isaac-art/Braidboard/3D/0119b/braidboardsmd v13.png

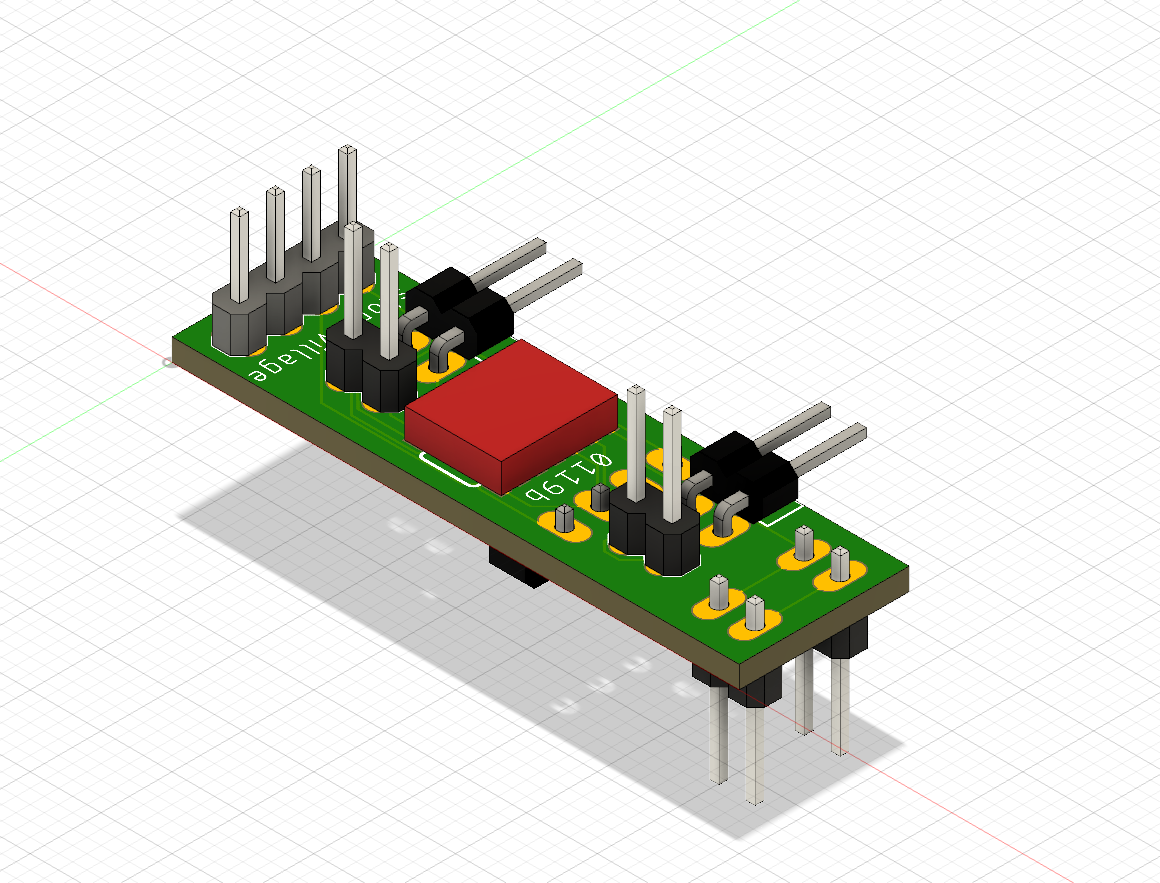
3D/0119b/braidboardsmd v13.png
