isaac-art/Braidboard/3D/0119b/mockup.png

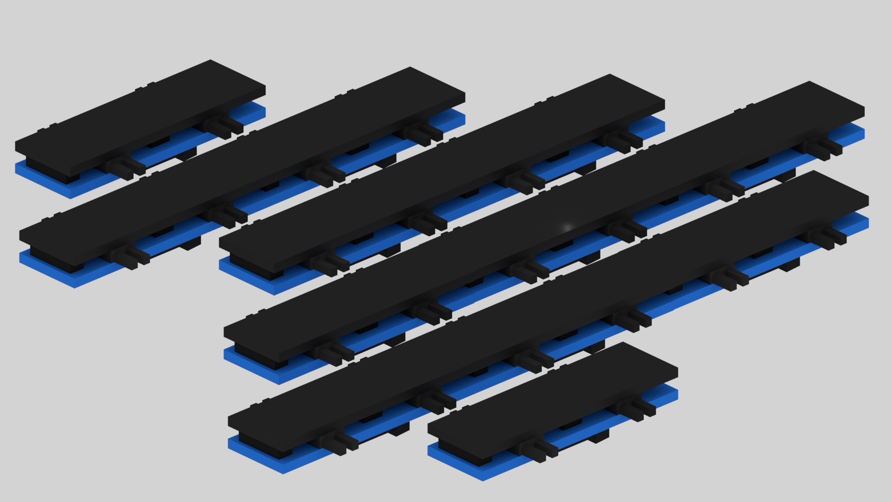
3D/0119b/mockup.png
