isaac-art/Braidboard/BOARD/0119b/braidboard_back.png

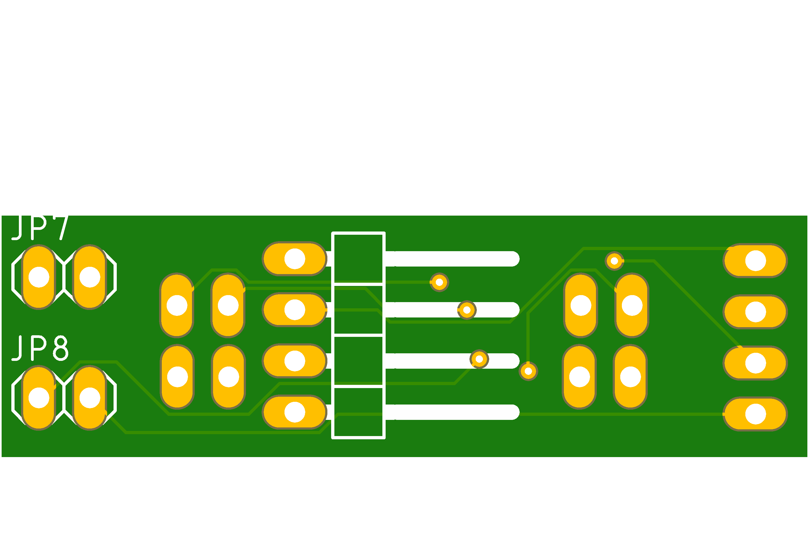
BOARD/0119b/braidboard_back.png
