isaac-art/Braidboard/BOARD/0119b/braidboard_front.png

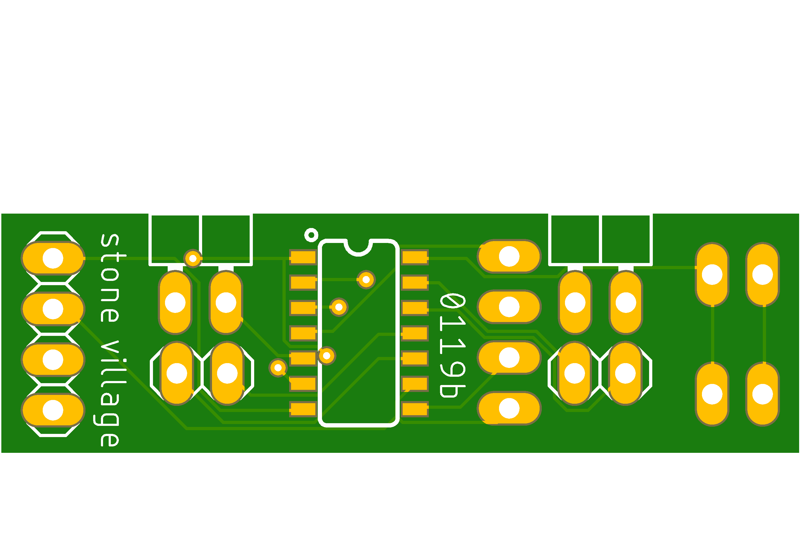
BOARD/0119b/braidboard_front.png
