isaac-art/Braidboard/PHOTOS/020119_250119/0119a.jpg

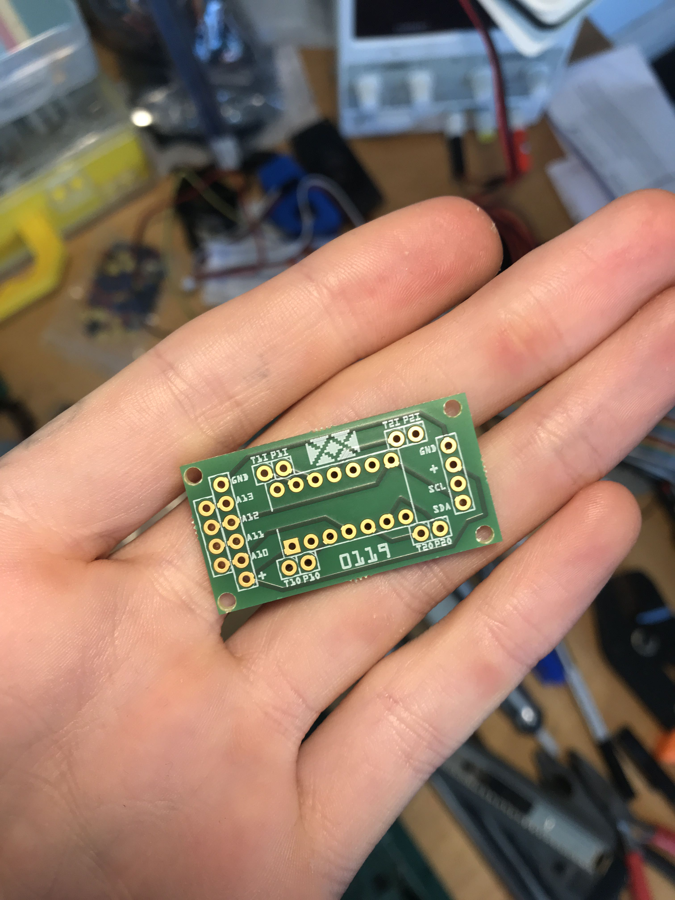
PHOTOS/020119_250119/0119a.jpg
