isaac-art/Braidboard/PHOTOS/020119_250119/IMG_2867.jpeg

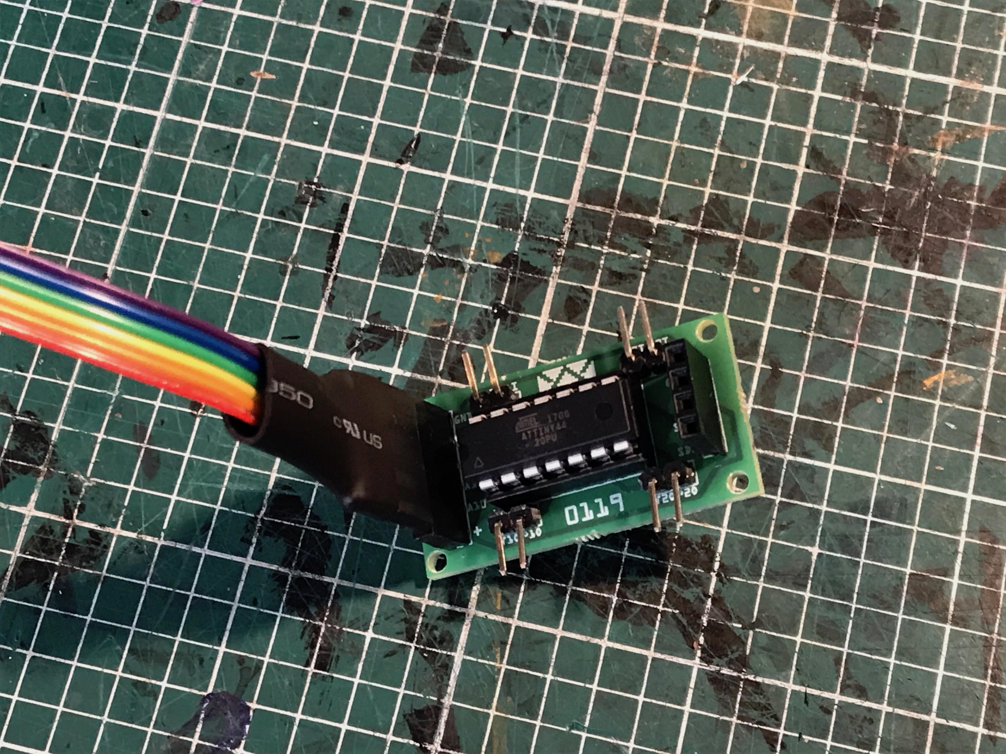
PHOTOS/020119_250119/IMG_2867.jpeg
