isaac-art/Braidboard/PHOTOS/020119_250119/IMG_2872.jpeg

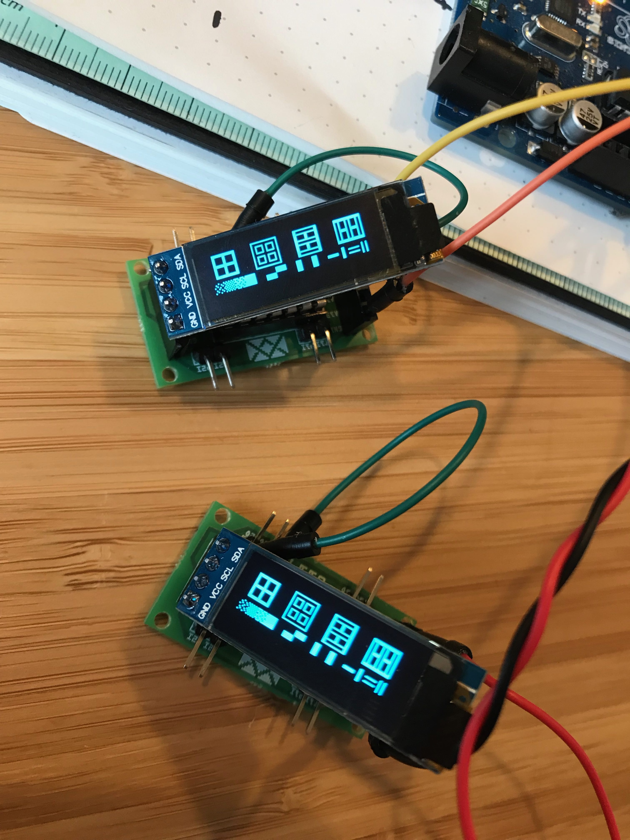
PHOTOS/020119_250119/IMG_2872.jpeg
