isaac-art/Braidboard/PHOTOS/020119_250119/IMG_2880.jpeg

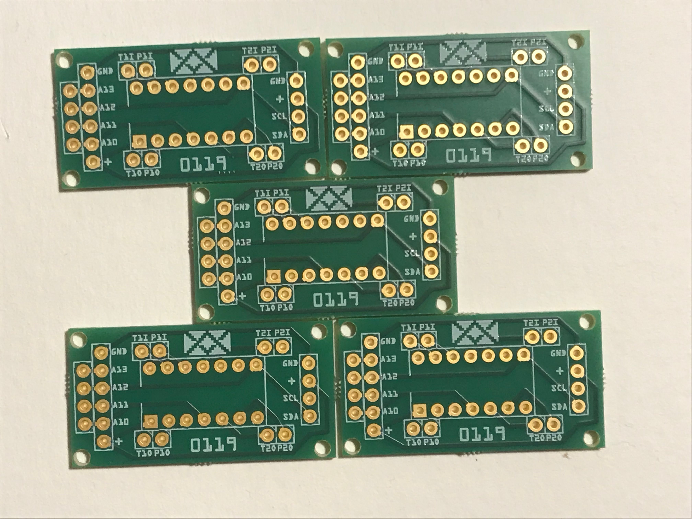
PHOTOS/020119_250119/IMG_2880.jpeg
