isaac-art/Braidboard/PHOTOS/020119_250119/IMG_2887.jpeg

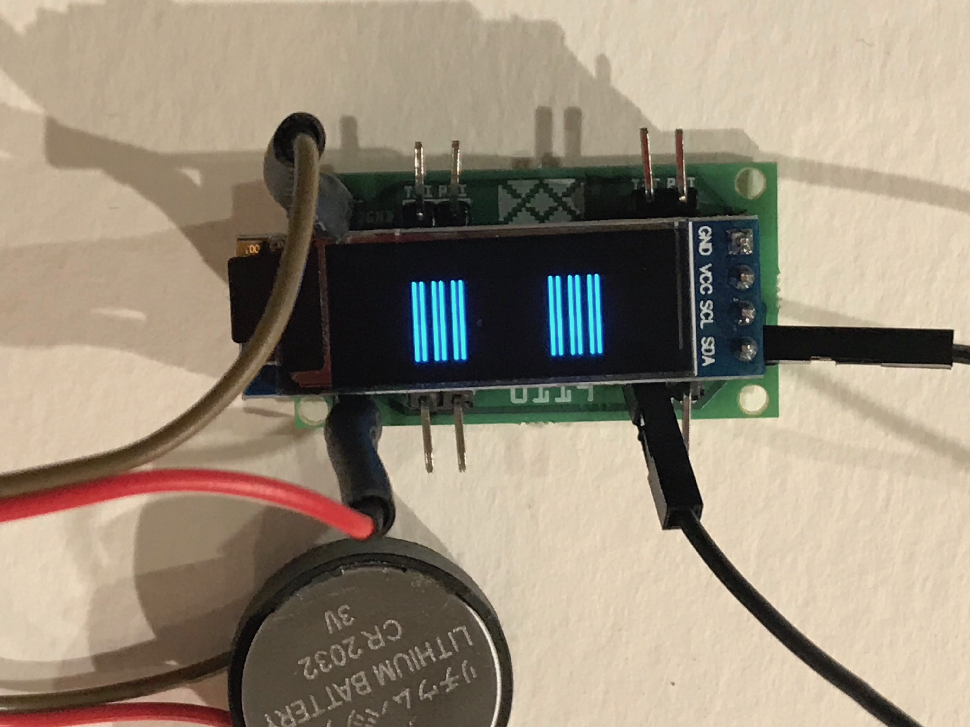
PHOTOS/020119_250119/IMG_2887.jpeg
