isaac-art/Braidboard/PHOTOS/260119_290119/IMG_2928.jpeg

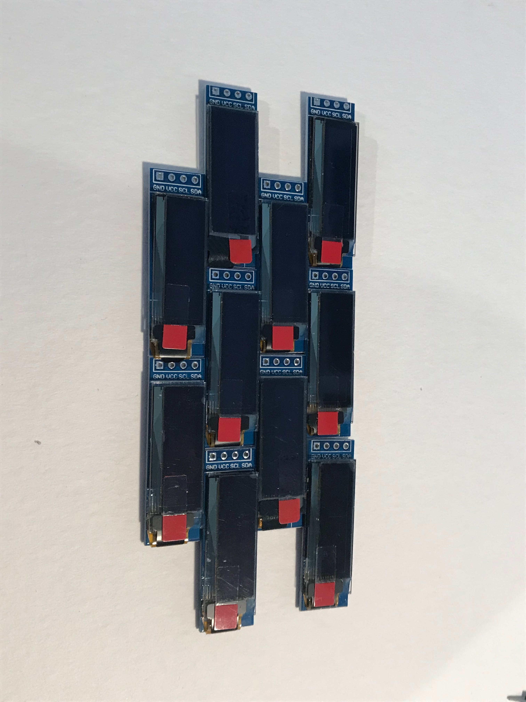
PHOTOS/260119_290119/IMG_2928.jpeg
