isaac-art/Braidboard/PHOTOS/260119_290119/IMG_2929.jpeg

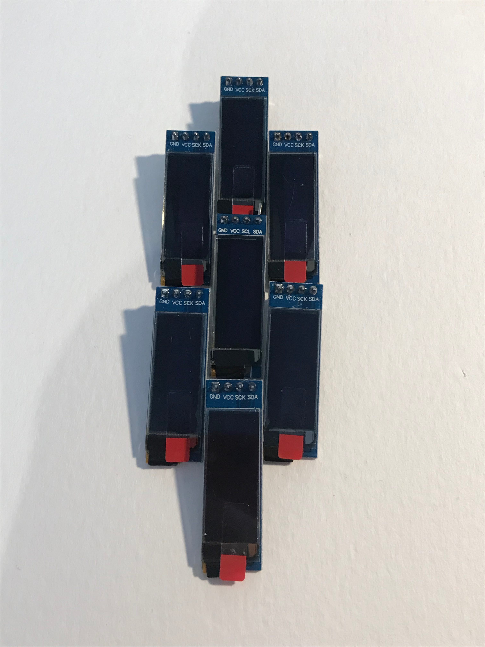
PHOTOS/260119_290119/IMG_2929.jpeg
