isaac-art/Braidboard/PHOTOS/260119_290119/IMG_2944.jpg

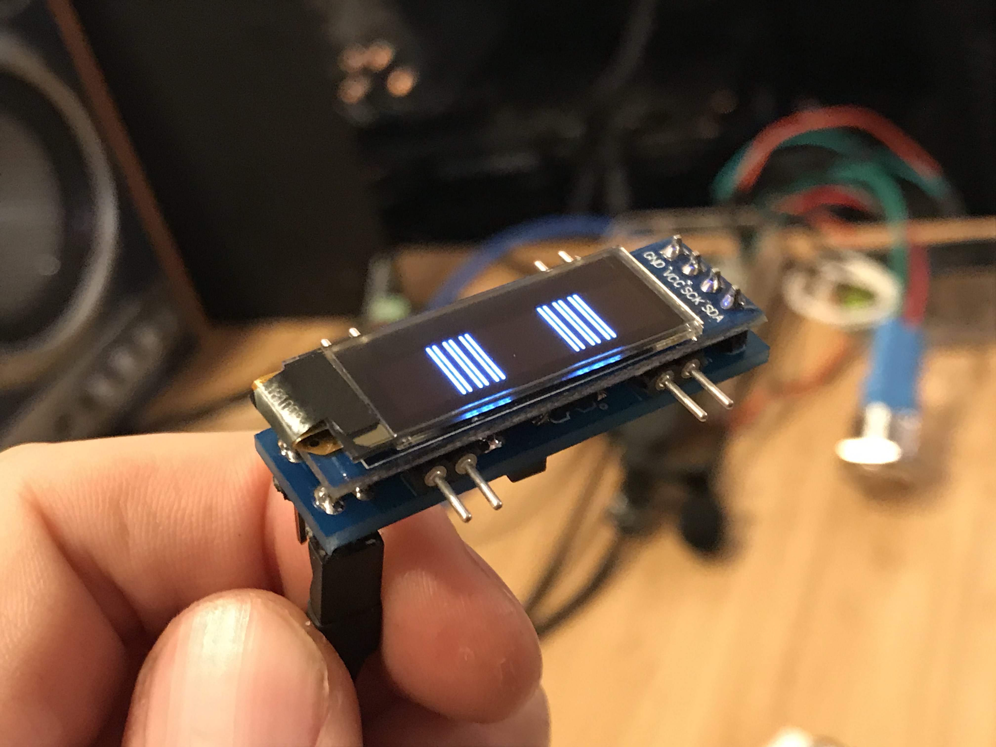
PHOTOS/260119_290119/IMG_2944.jpg
