isaac-art/Braidboard/PHOTOS/300119_010219/IMG_2962.jpeg

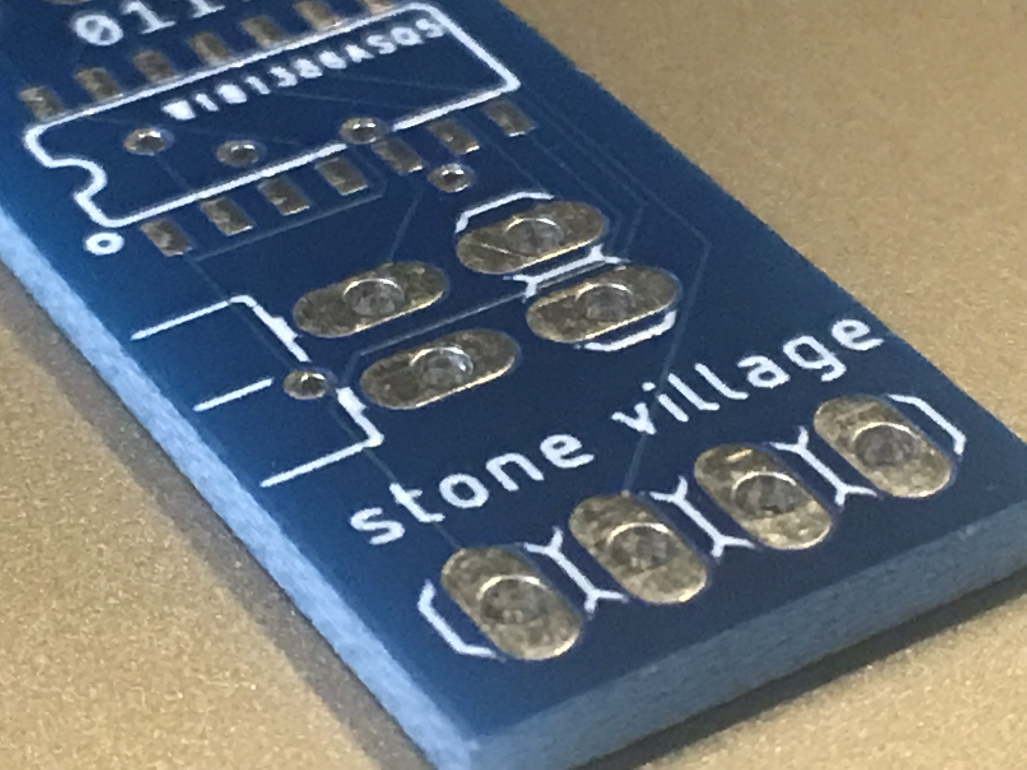
PHOTOS/300119_010219/IMG_2962.jpeg
