isaac-art/Braidboard/PHOTOS/300119_010219/IMG_2984.jpeg

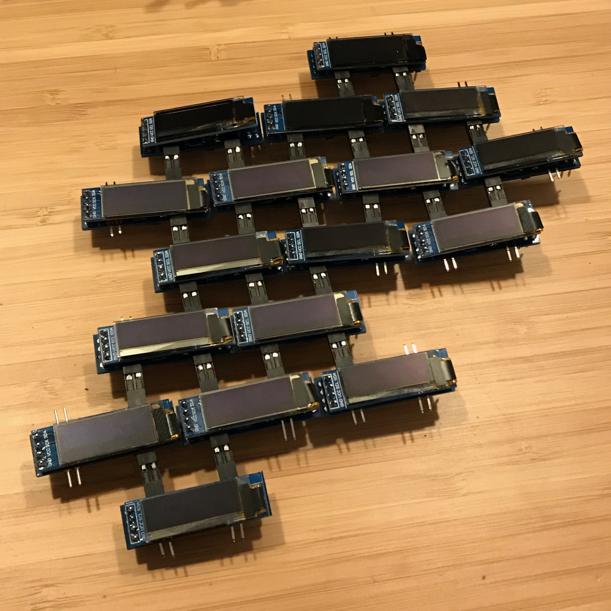
PHOTOS/300119_010219/IMG_2984.jpeg
