isaac-art/Braidboard/PHOTOS/300119_010219/IMG_3001.jpg

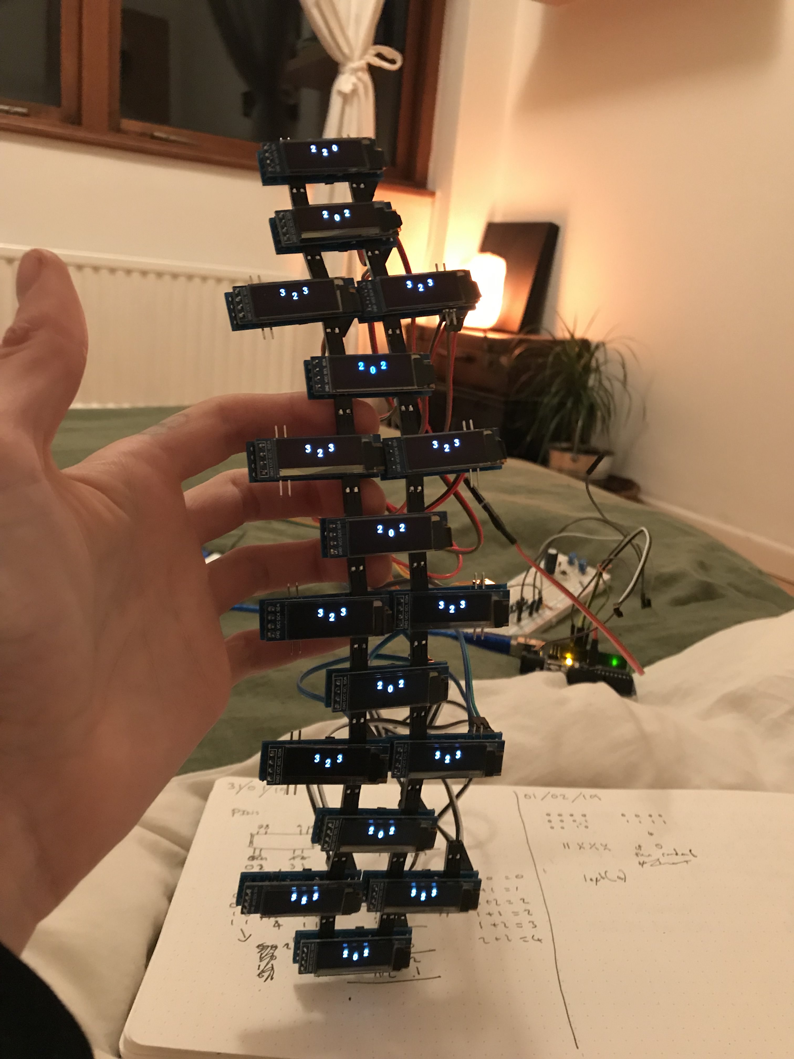
PHOTOS/300119_010219/IMG_3001.jpg
