isaac-art/Braidboard/PHOTOS/300119_010219/IMG_3003.jpeg

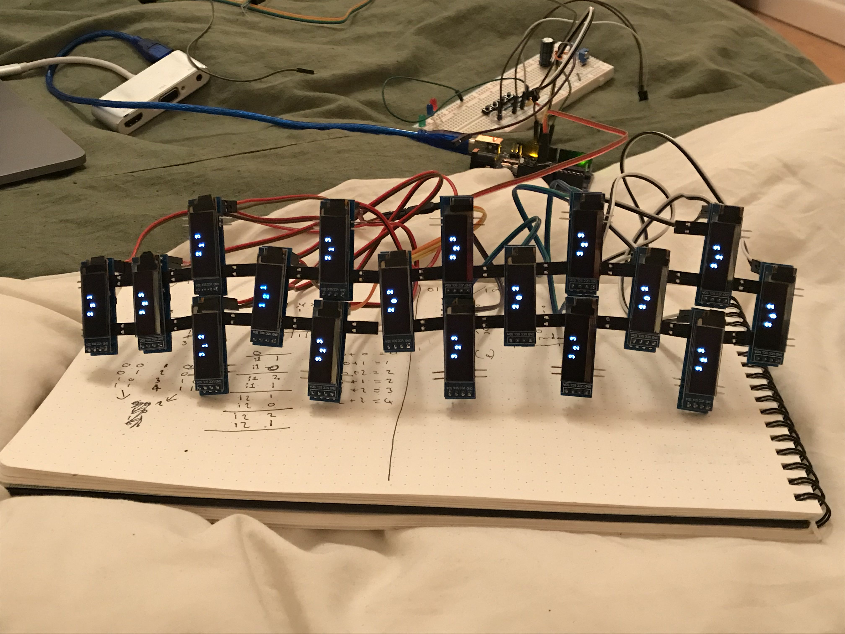
PHOTOS/300119_010219/IMG_3003.jpeg
