isaac-art/Braidboard/RESEARCH/2xmcp20317-i2c.jpg

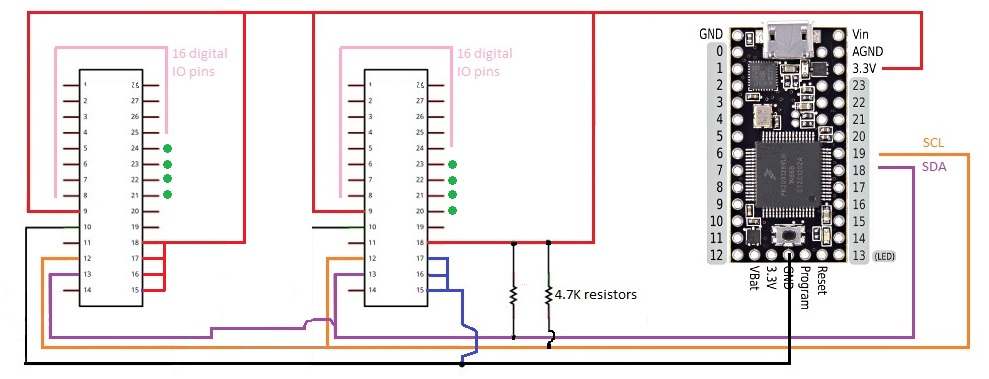
RESEARCH/2xmcp20317-i2c.jpg
