isaac-art/Braidboard/RESEARCH/52713d5b757b7fc0658b4567.png

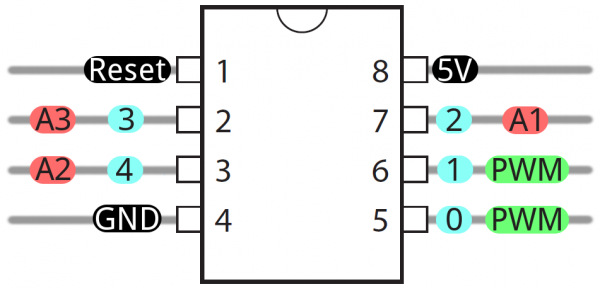
RESEARCH/52713d5b757b7fc0658b4567.png
