isaac-art/Braidboard/RESEARCH/Circuit-using-A3144-Hall-effect-Sensor.png

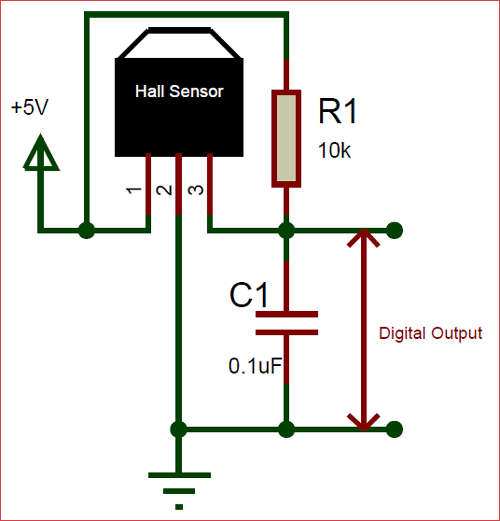
RESEARCH/Circuit-using-A3144-Hall-effect-Sensor.png
