isaac-art/Braidboard/RESEARCH/download-1.png

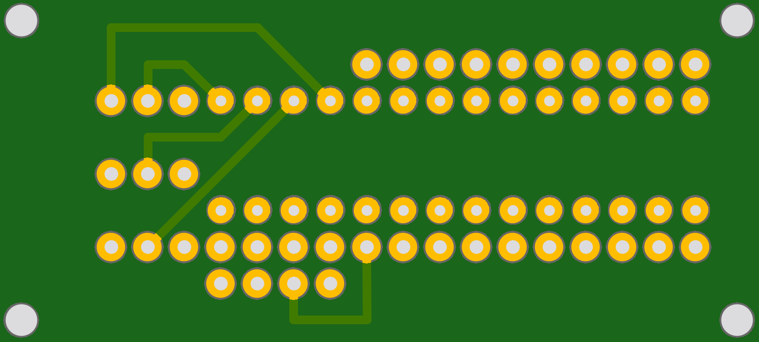
RESEARCH/download-1.png
