isaac-art/Braidboard/RESEARCH/download.png

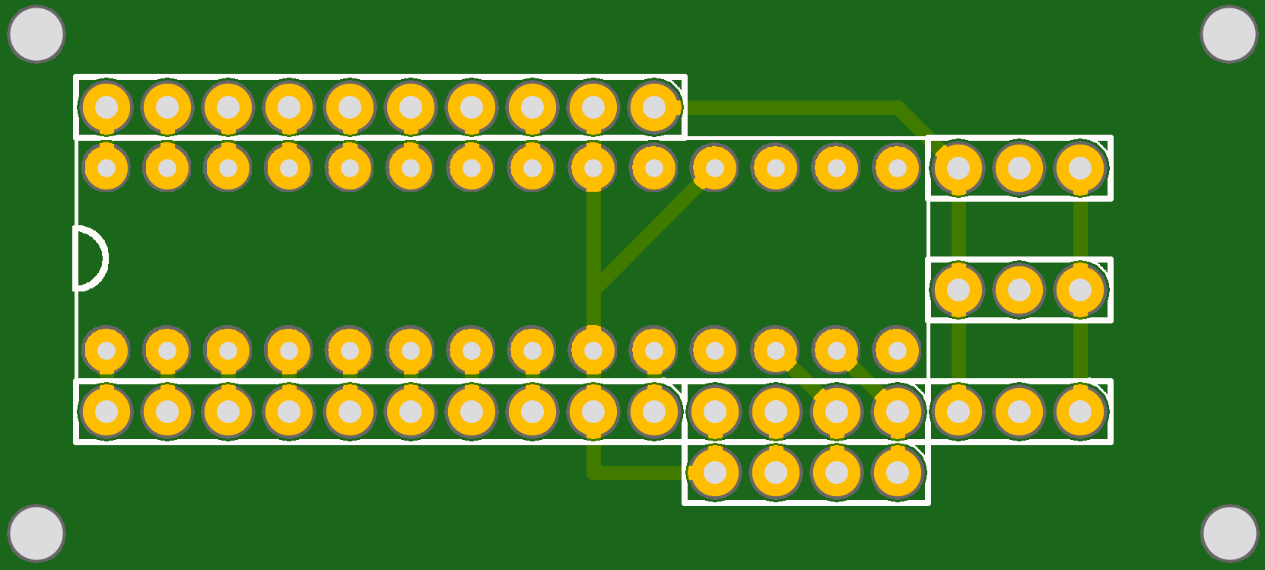
RESEARCH/download.png
