isaac-art/Braidboard/RESEARCH/proxy.duckduckgo.jpg

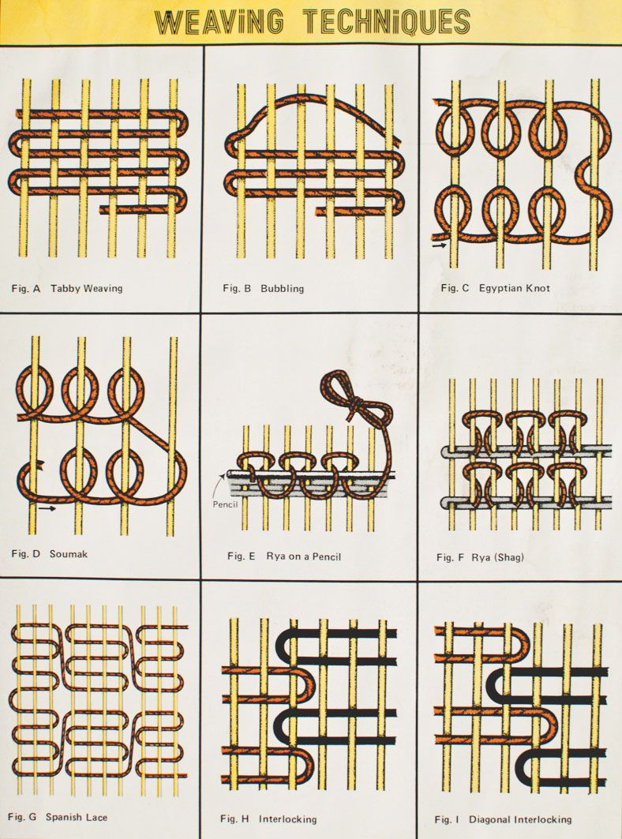
RESEARCH/proxy.duckduckgo.jpg
