isaac-art/Braidboard/RESEARCH/s-l1600.jpg

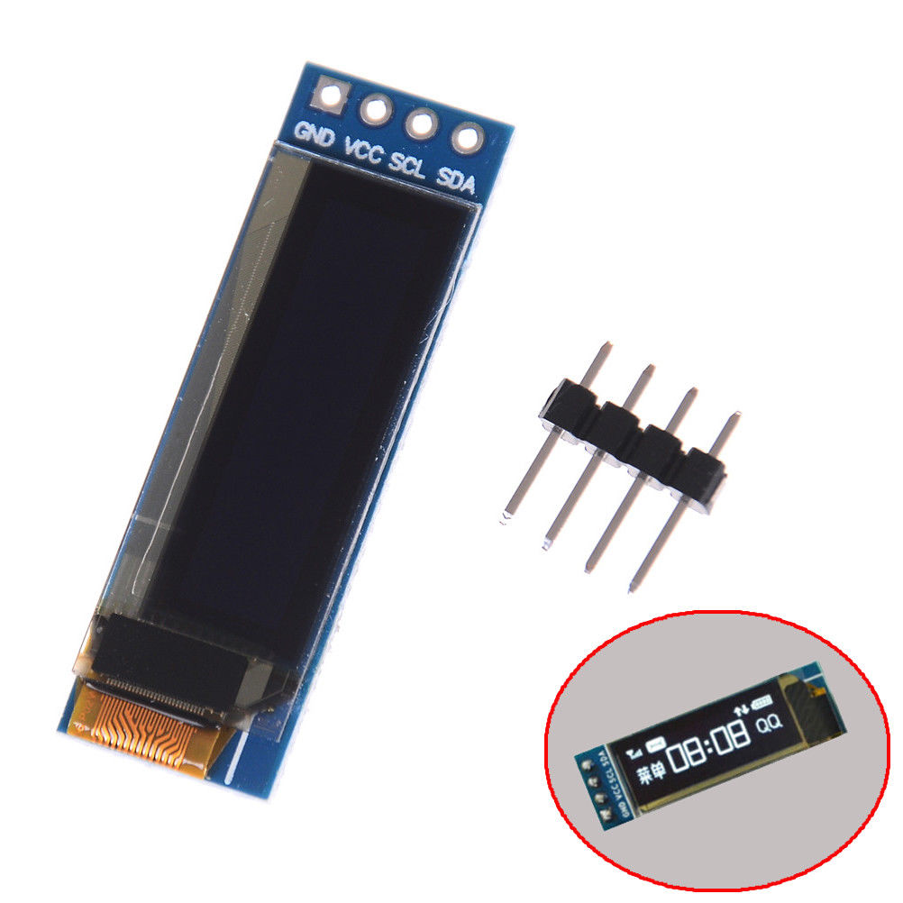
RESEARCH/s-l1600.jpg
