isaac-art/Braidboard/RESEARCH/Screenshot-from-2019-01-06-10-55-49.png

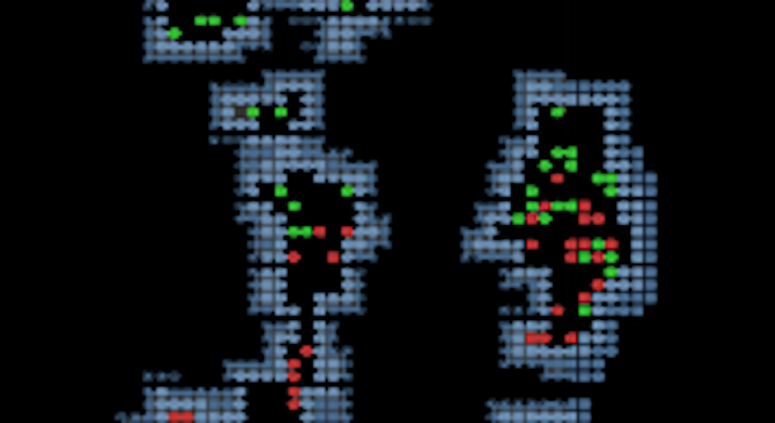
RESEARCH/Screenshot-from-2019-01-06-10-55-49.png
