isaac-art/Braidboard/RESEARCH/usbscope-tiny-top.png

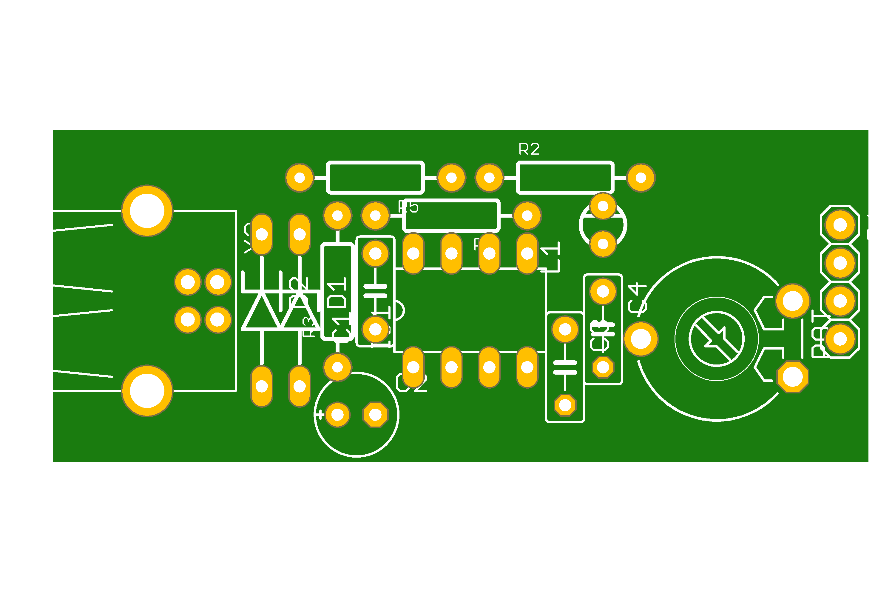
RESEARCH/usbscope-tiny-top.png
