isaac-art/Braidboard/SKETCHBOOK/020119_250119/Image 5.jpeg

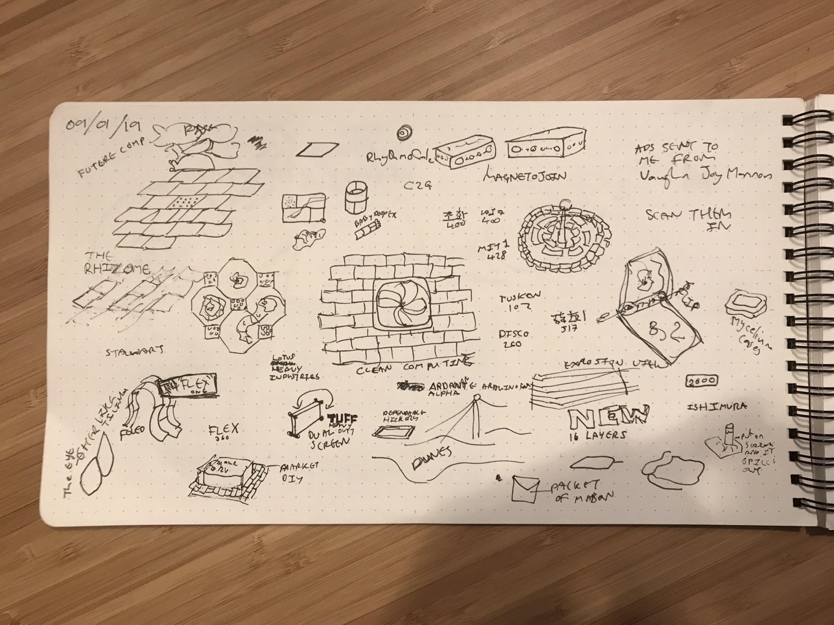
SKETCHBOOK/020119_250119/Image 5.jpeg
