isaac-art/Braidboard/SKETCHBOOK/020119_250119/Image 7.jpeg

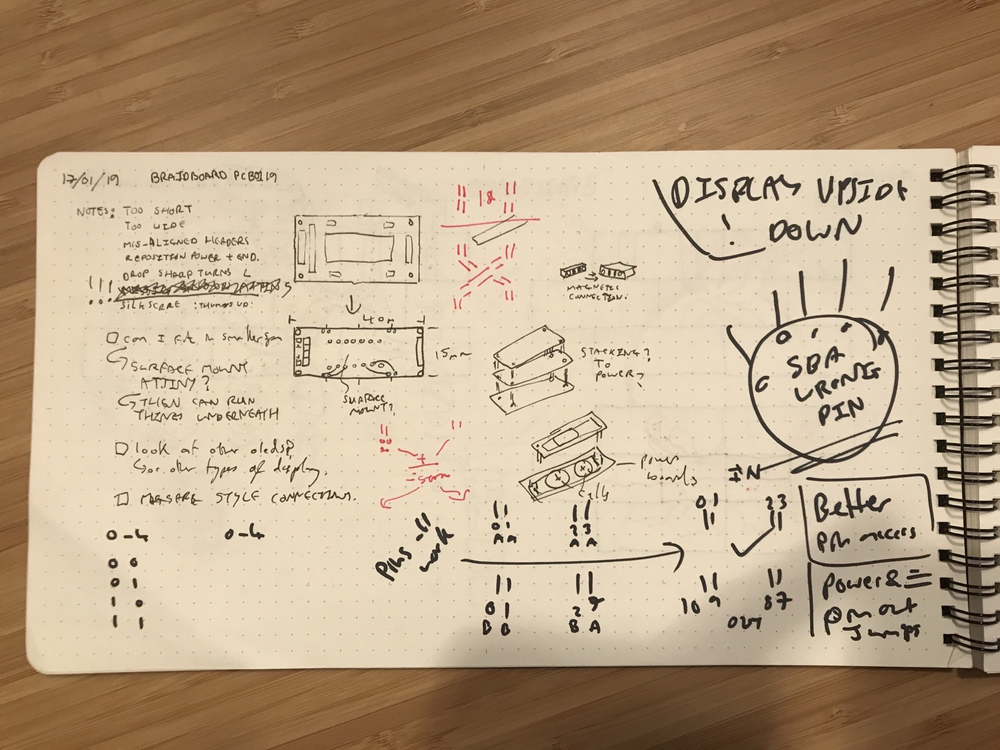
SKETCHBOOK/020119_250119/Image 7.jpeg
