isaac-art/Braidboard/SKETCHBOOK/020119_250119/Image 10.jpeg

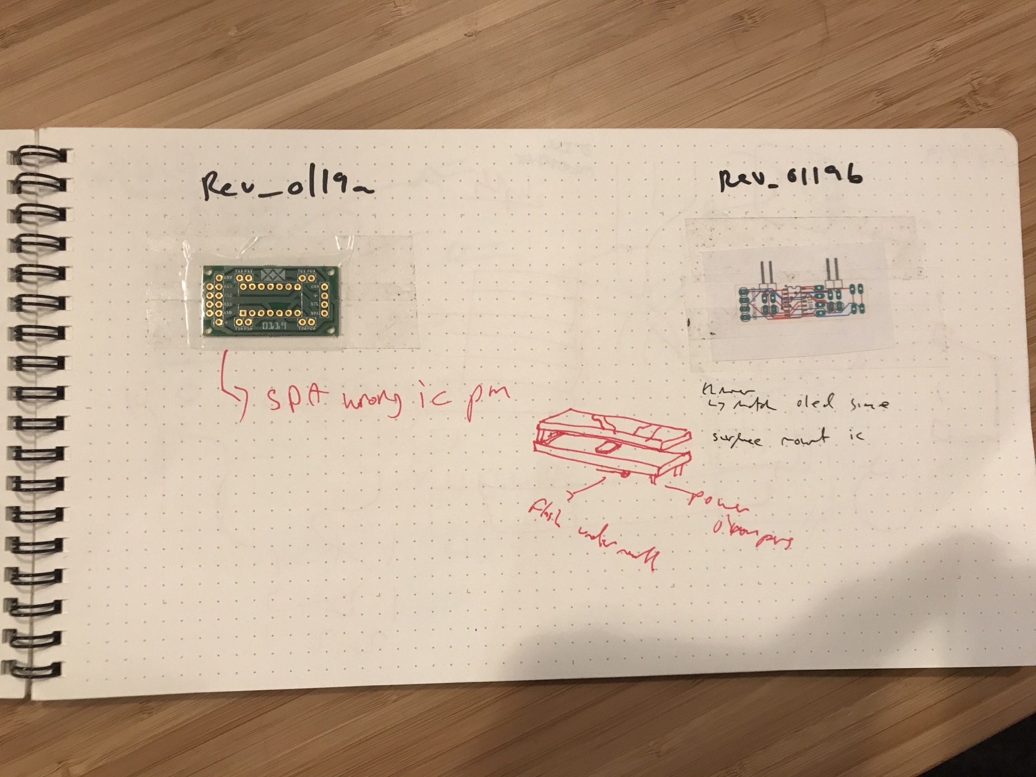
SKETCHBOOK/020119_250119/Image 10.jpeg
