isaac-art/Braidboard/SKETCHBOOK/020119_250119/Image 12.jpeg

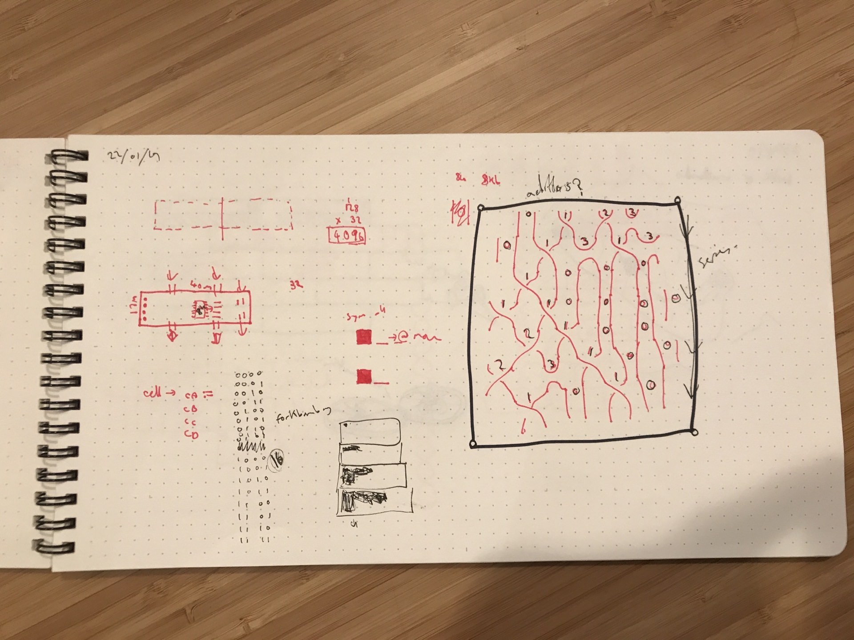
SKETCHBOOK/020119_250119/Image 12.jpeg
