isaac-art/Braidboard/SKETCHBOOK/020119_250119/Image.jpeg

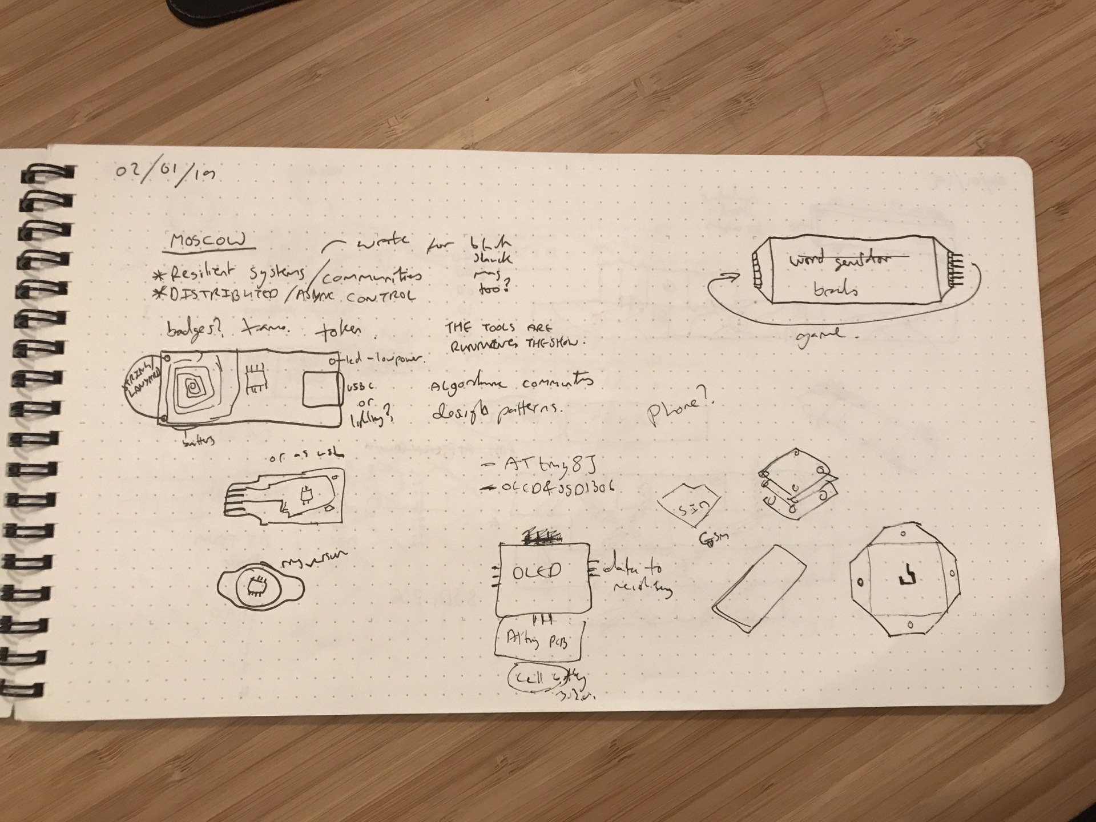
SKETCHBOOK/020119_250119/Image.jpeg
