isaac-art/Braidboard/SKETCHBOOK/020219_080219/Image 3.jpeg

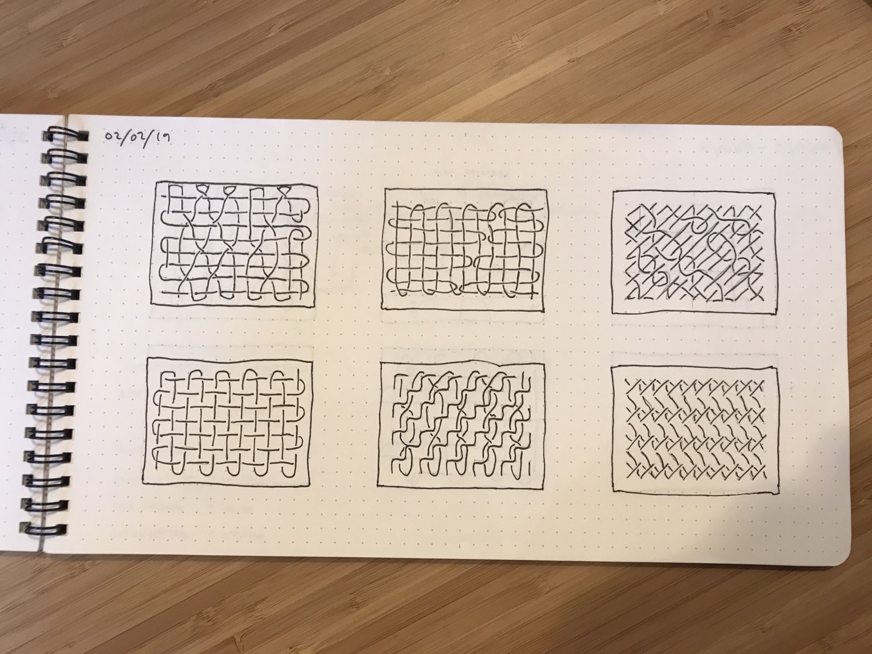
SKETCHBOOK/020219_080219/Image 3.jpeg
