isaac-art/Braidboard/SKETCHBOOK/020219_080219/Image 5.jpeg

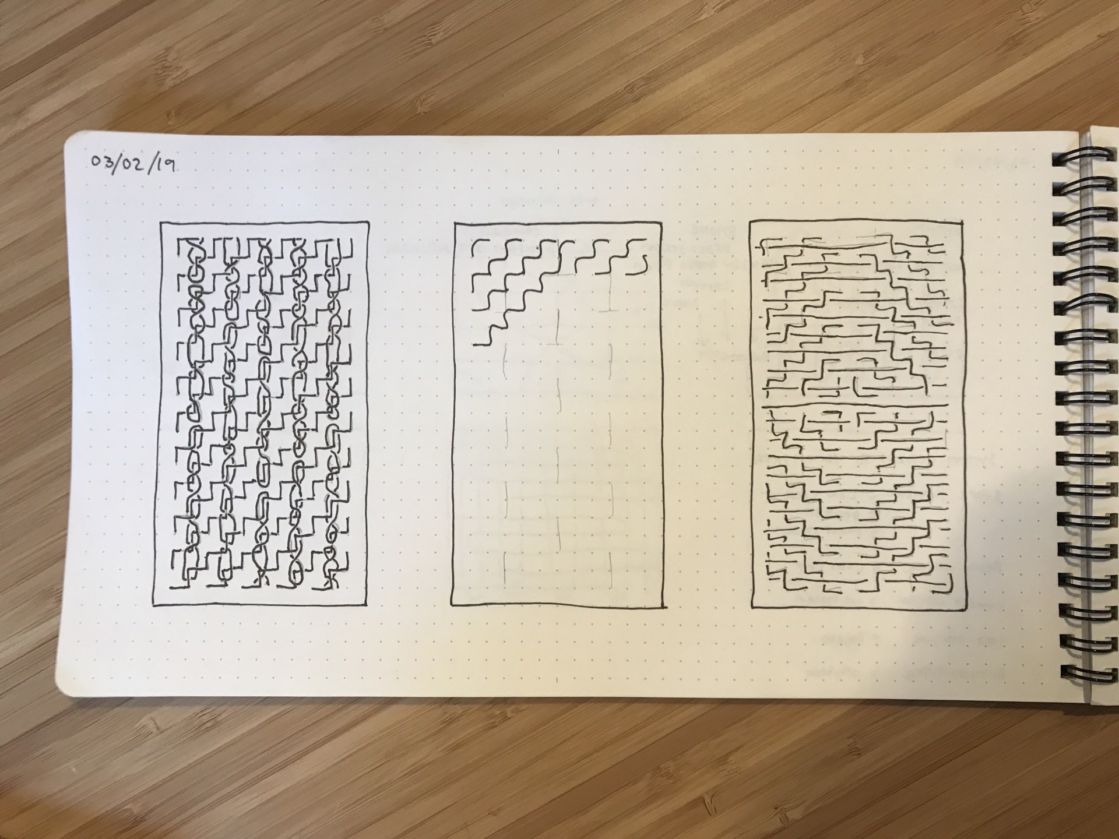
SKETCHBOOK/020219_080219/Image 5.jpeg
