isaac-art/Braidboard/SKETCHBOOK/020219_080219/Image 6.jpeg

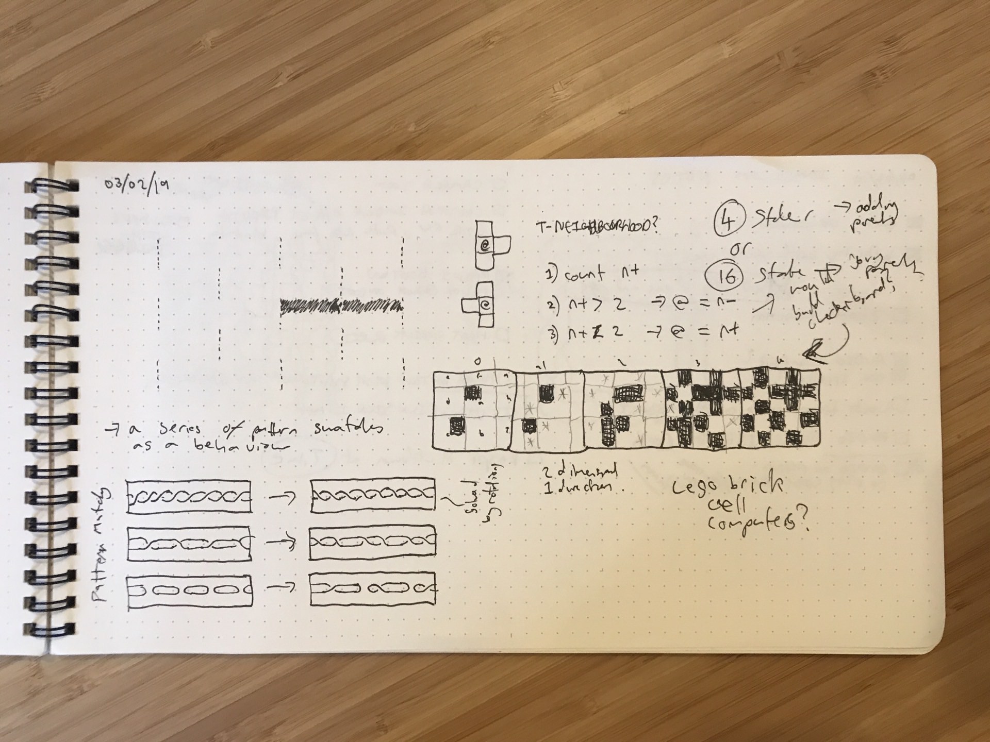
SKETCHBOOK/020219_080219/Image 6.jpeg
