isaac-art/Braidboard/SKETCHBOOK/020219_080219/Image 7.jpeg

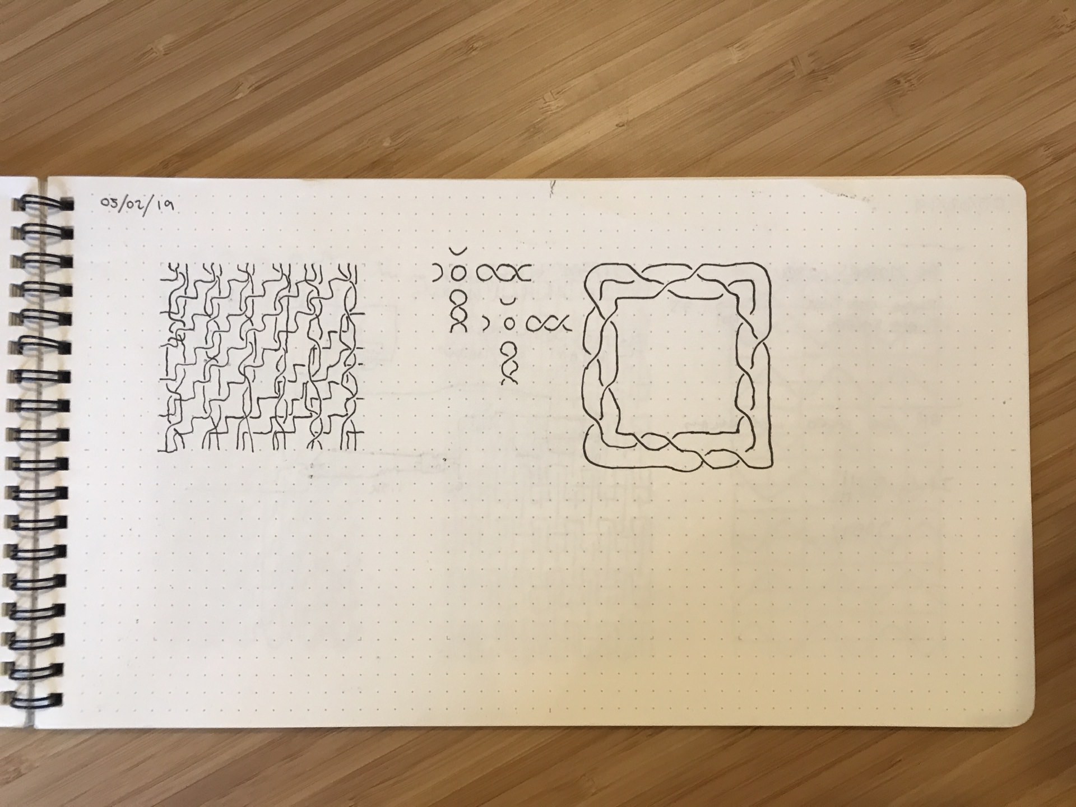
SKETCHBOOK/020219_080219/Image 7.jpeg
