isaac-art/Braidboard/SKETCHBOOK/300119_010219/Image2.jpeg

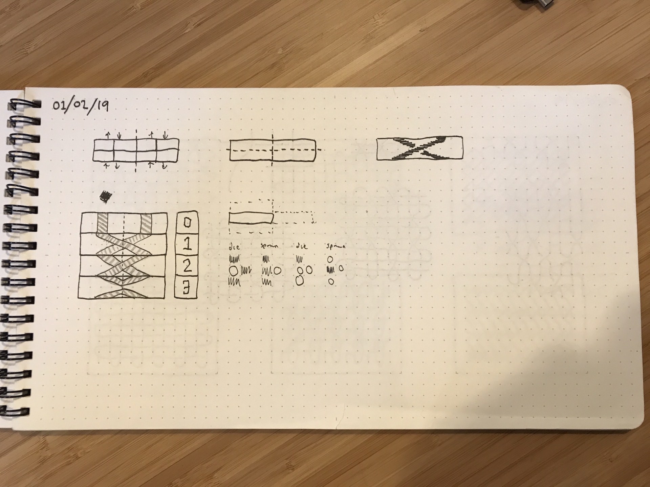
SKETCHBOOK/300119_010219/Image2.jpeg
