isaac-art/Braidboard/SKETCHBOOK/300119_010219/Image.jpeg

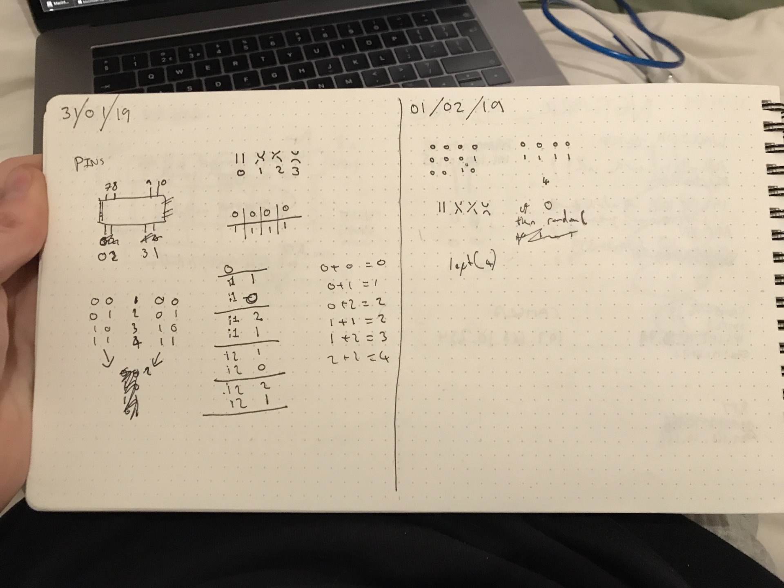
SKETCHBOOK/300119_010219/Image.jpeg
