isaac-art/Braidboard/PHOTOS/020119_250119/0119a_duo.jpg

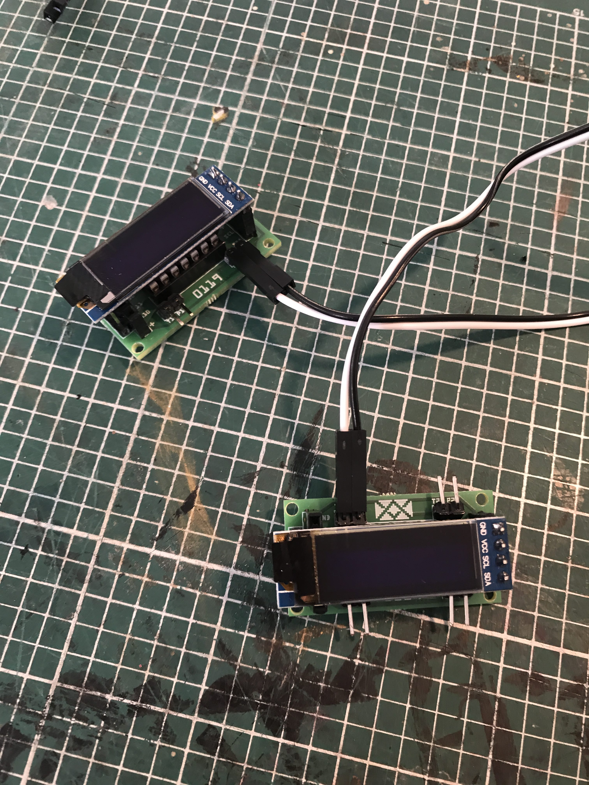
PHOTOS/020119_250119/0119a_duo.jpg
